cristianritter/EnergyMeter/DOCS/Medicoes/IMG_20200415_194022.jpg

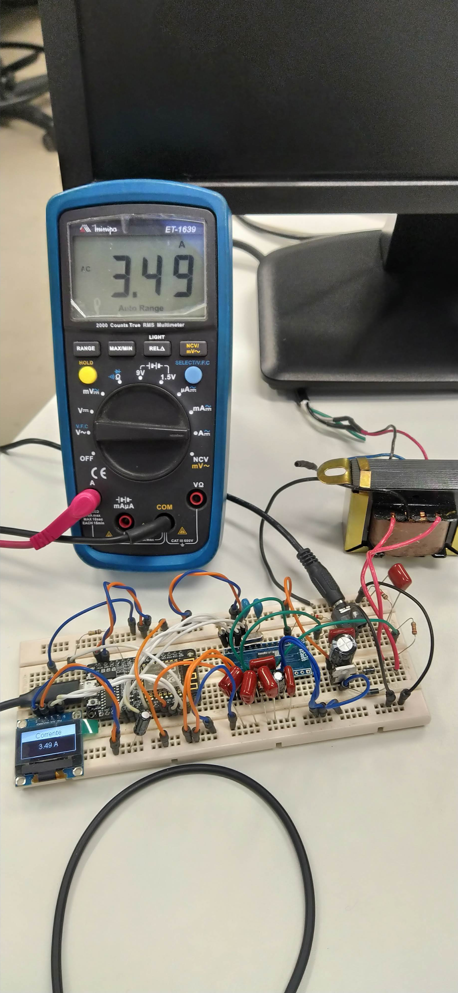
DOCS/Medicoes/IMG_20200415_194022.jpg
