cristianritter/EnergyMeter/DOCS/Medicoes/IMG_20200416_145322.jpg

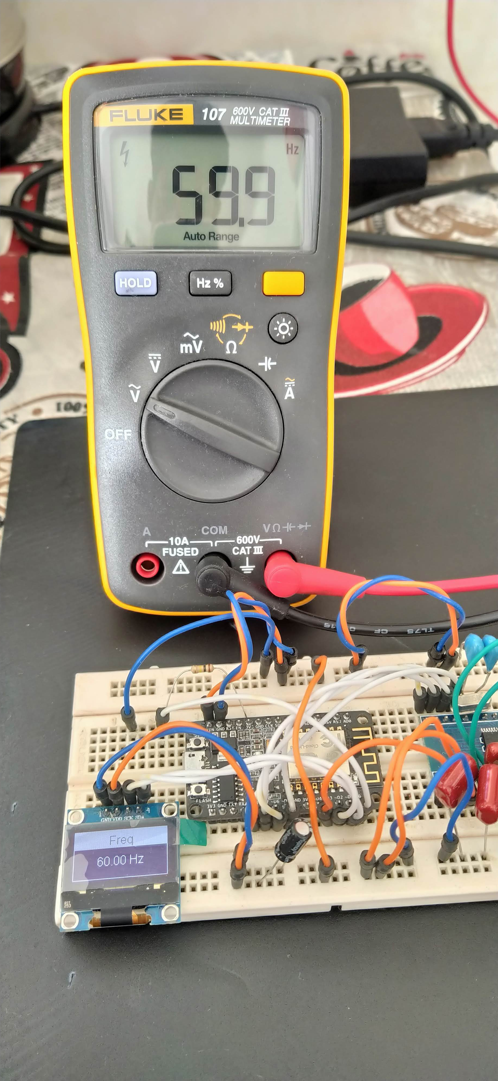
DOCS/Medicoes/IMG_20200416_145322.jpg
